mysens-cn/kt82tvw/doc/Mysenso-QQ.png

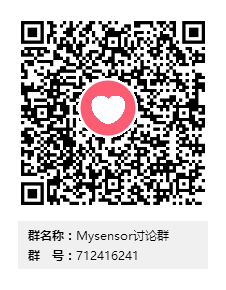
doc/Mysenso-QQ.png
