mysens-cn/kt82tvw/doc/package/AM312.jpg

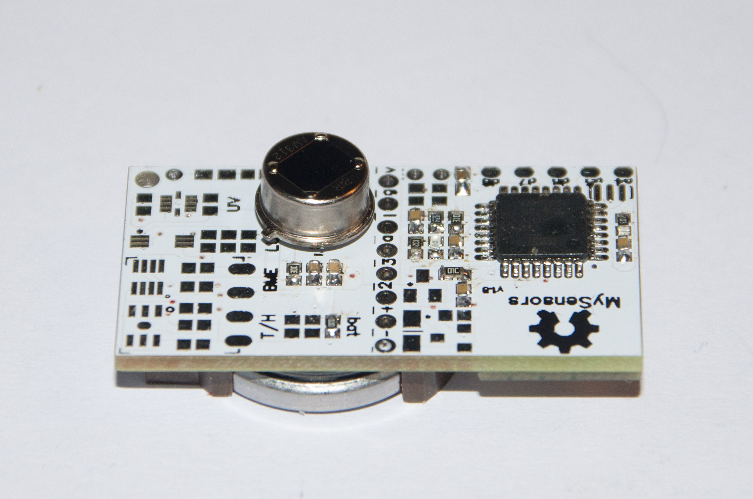
doc/package/AM312.jpg
