mysens-cn/kt82tvw/doc/package/back.jpg

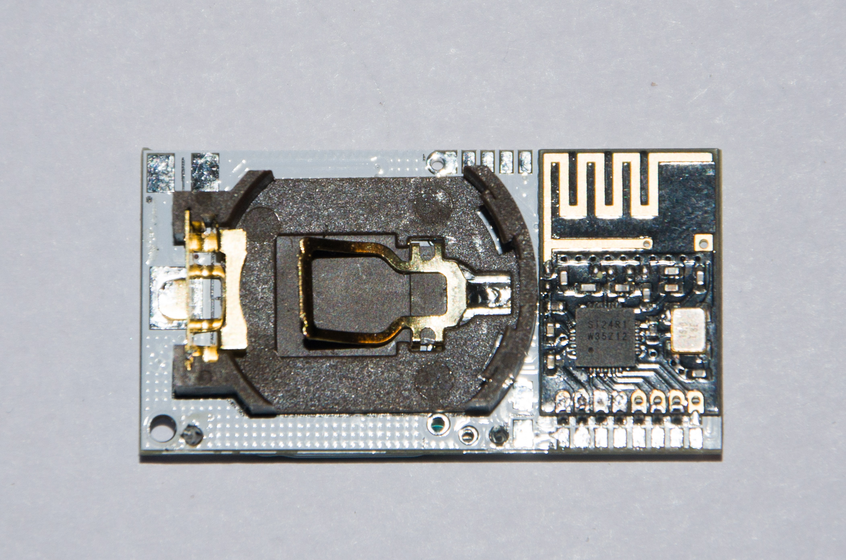
doc/package/back.jpg
