mysens-cn/kt82tvw/doc/package/BH1750.jpg

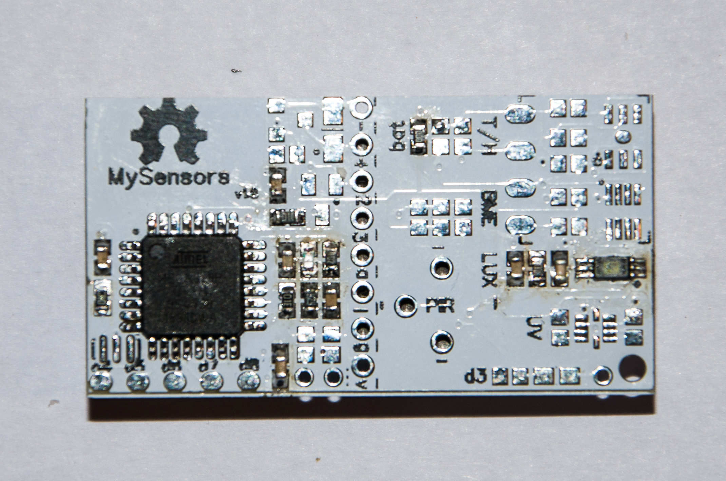
doc/package/BH1750.jpg
