mysens-cn/kt82tvw/doc/package/FLASH.jpg

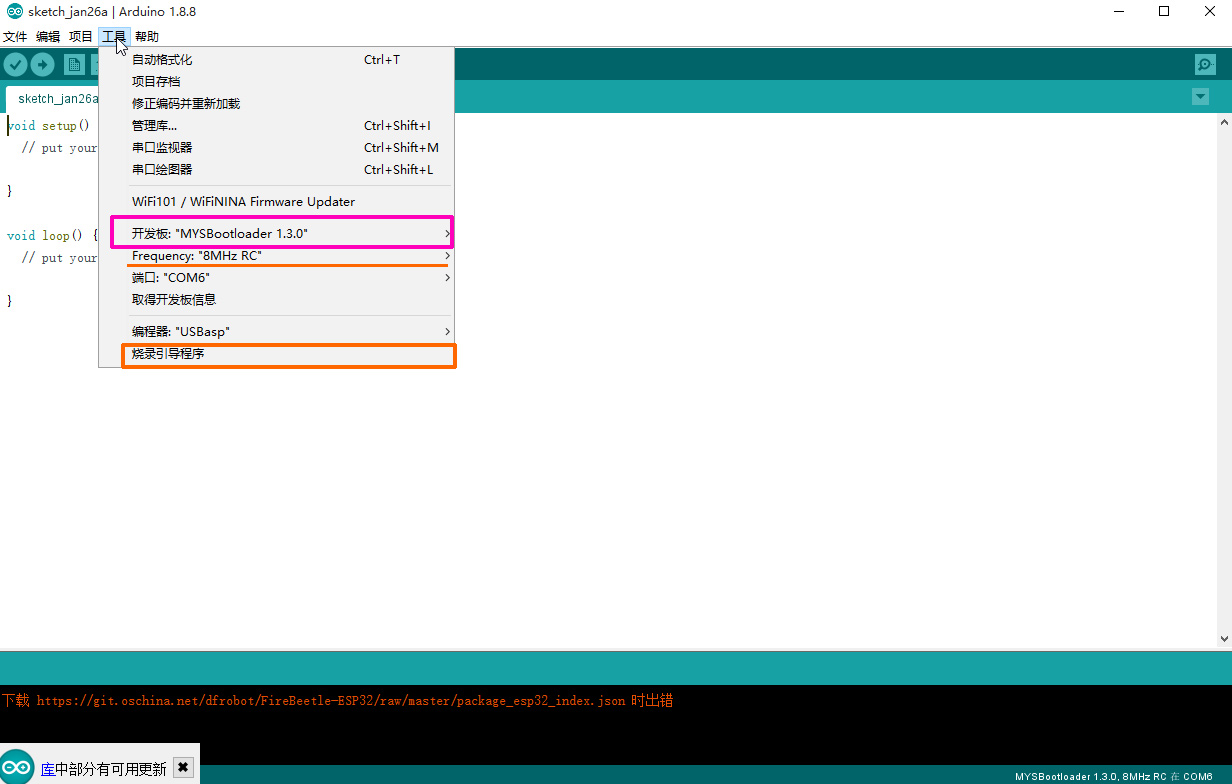
doc/package/FLASH.jpg
