mysens-cn/kt82tvw/doc/package/USBASP.jpg

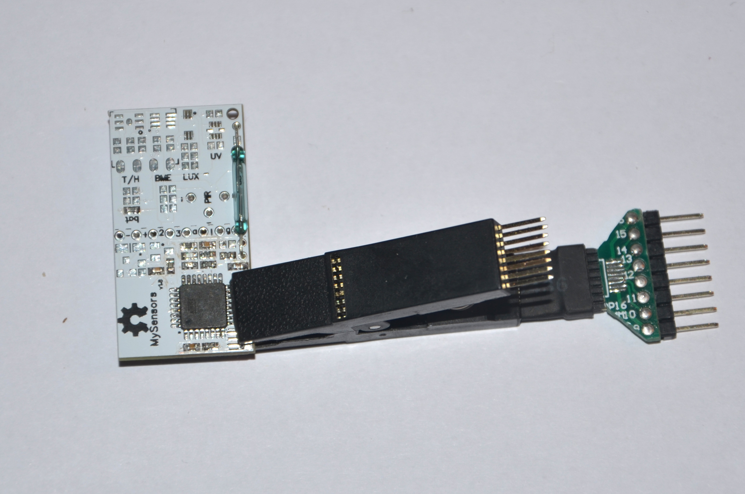
doc/package/USBASP.jpg
