mysens-cn/kt82tvw/doc/TTL+USBASP.jpg

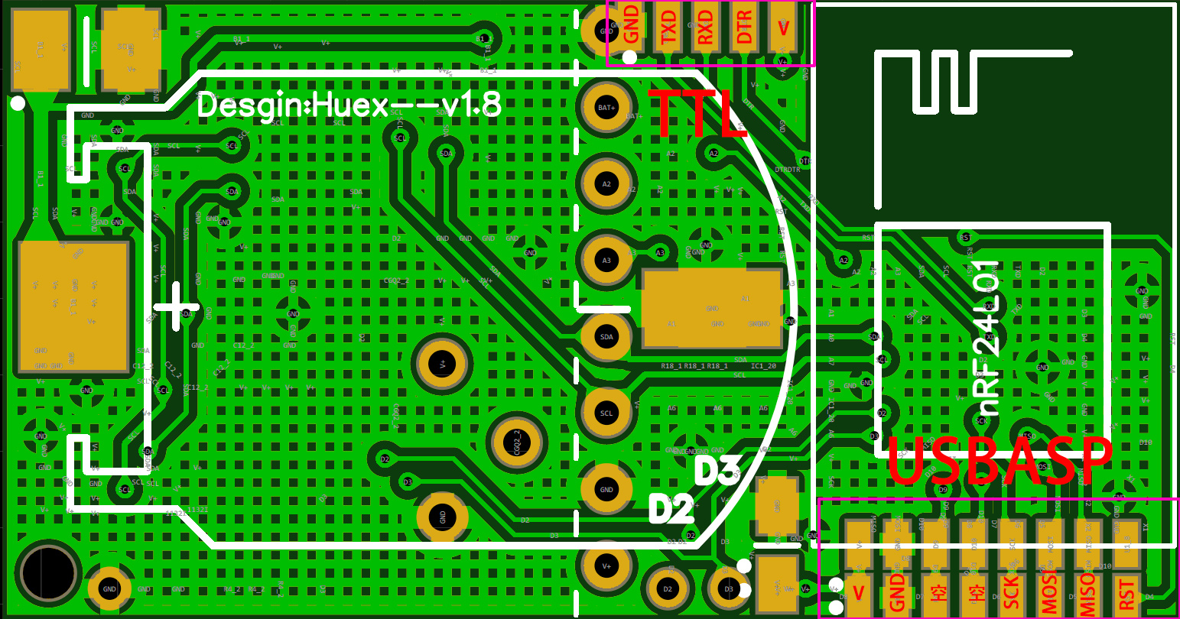
doc/TTL+USBASP.jpg
